Heartland-Data/esp32-mintia-sensor-kit/test/double/driver/i2c_master.c

/**
 * @file i2c_master.c
 * @brief ESP-IDF I2C マスタードライバ テストダブル 実装
 * @copyright Copyright (C) 2026, Heartland Data inc. All Rights Reserved.
 * SPDX-FileCopyrightText: 2026 Heartland Data inc.
 * SPDX-License-Identifier: Apache-2.0
 */

#include "i2c_master.h"

esp_err_t i2c_master_bus_rm_device(i2c_master_dev_handle_t handle)
{
    return ESP_OK;
}

esp_err_t i2c_del_master_bus(i2c_master_bus_handle_t bus_handle)
{
    return ESP_OK;
}

esp_err_t i2c_new_master_bus(const i2c_master_bus_config_t *bus_config, i2c_master_bus_handle_t *ret_bus_handle)
{
    return ESP_OK;
}

esp_err_t i2c_master_bus_add_device(i2c_master_bus_handle_t bus_handle, const i2c_device_config_t *dev_config, i2c_master_dev_handle_t *ret_handle)
{
    return ESP_OK;
}
